Astronuat21/4DS/Images/CTRL_L/Left_Controls_Back.png

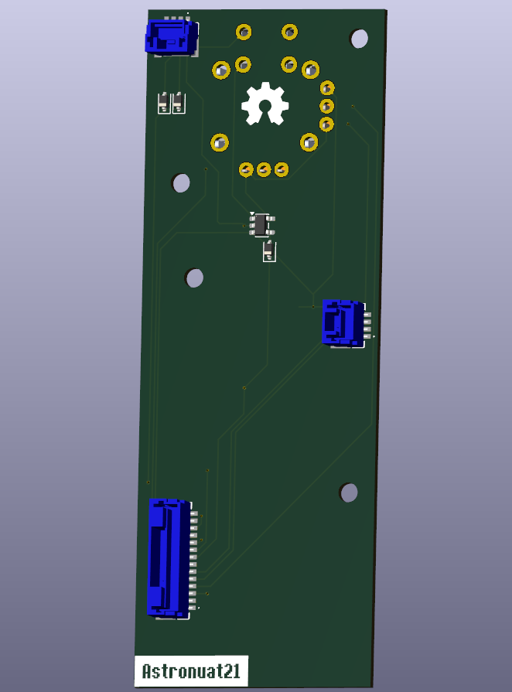
Images/CTRL_L/Left_Controls_Back.png
