Astronuat21/4DS/Images/CTRL_L/Left_Controls_PCB.png

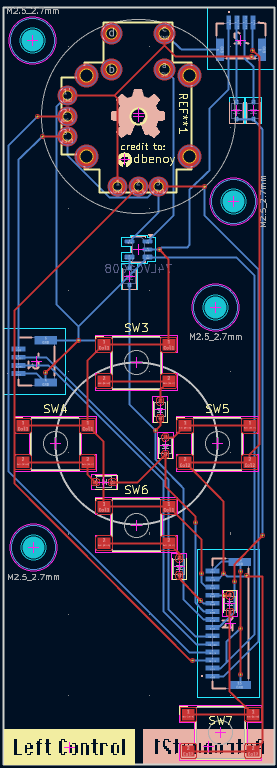
Images/CTRL_L/Left_Controls_PCB.png
