Astronuat21/4DS/Images/CTRL_R/Right_Controls_Back.png

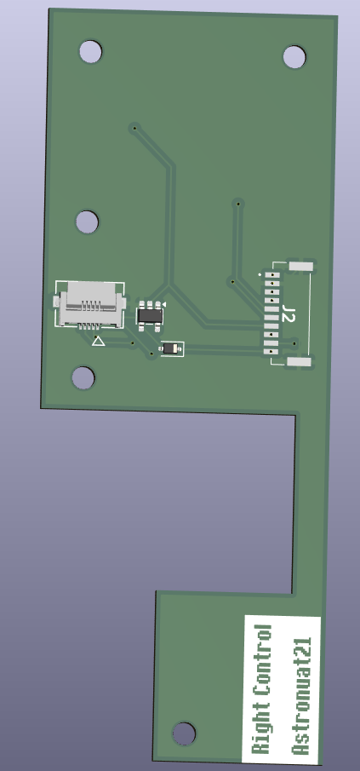
Images/CTRL_R/Right_Controls_Back.png
