Astronuat21/4DS/Images/Motherboard/PCB_Wifi_05_12_26.png

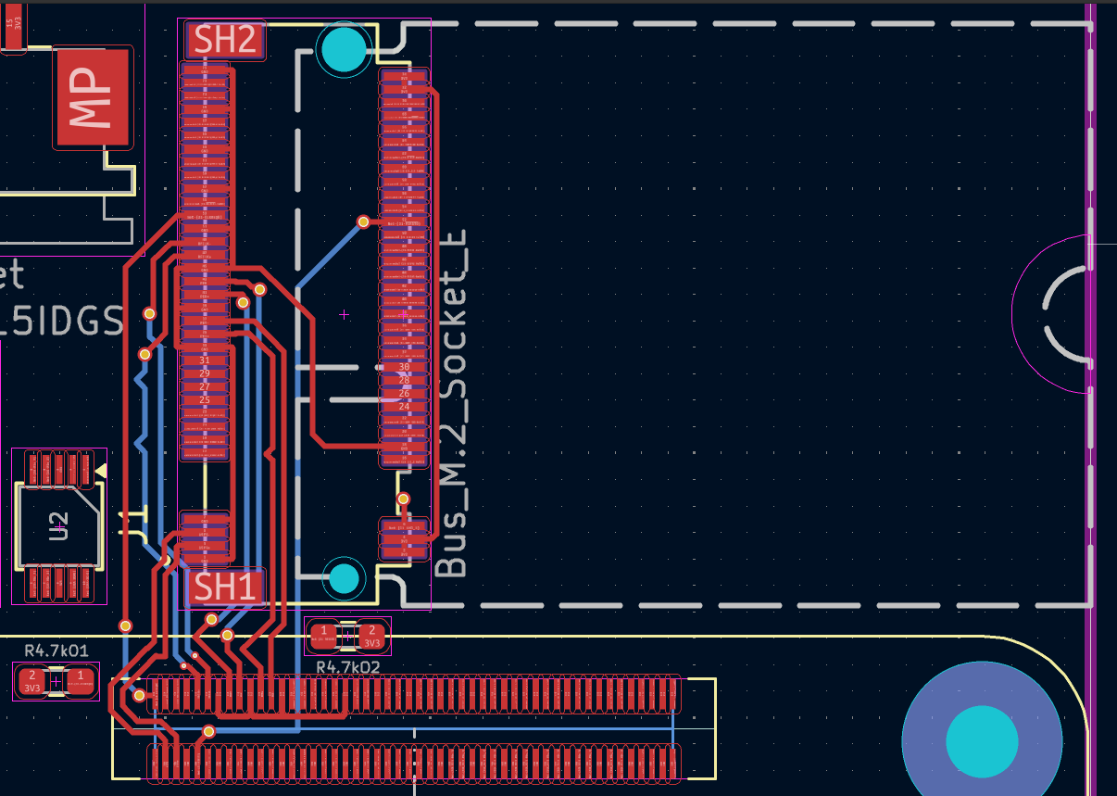
Images/Motherboard/PCB_Wifi_05_12_26.png
