Astronuat21/4DS/Images/Other/4DSPowerPath.png

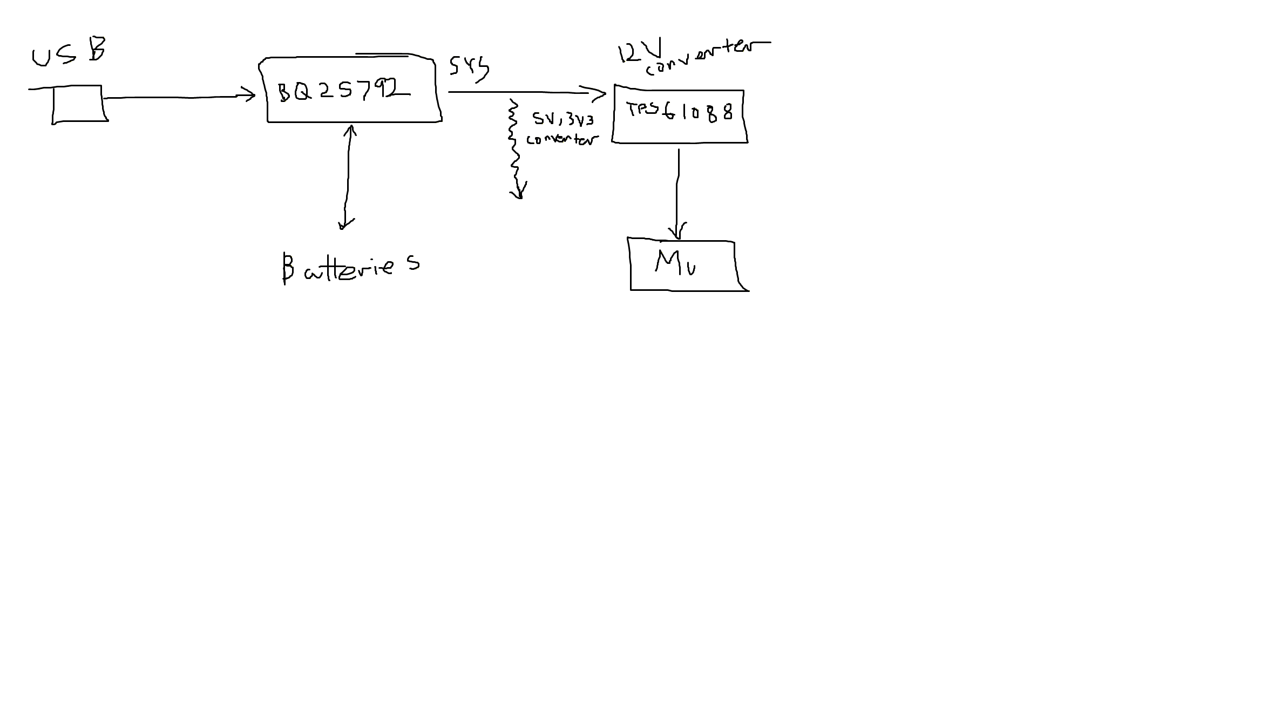
Images/Other/4DSPowerPath.png
