Astronuat21/4DS/Motherboard/3D_models/MDT420M02001.step

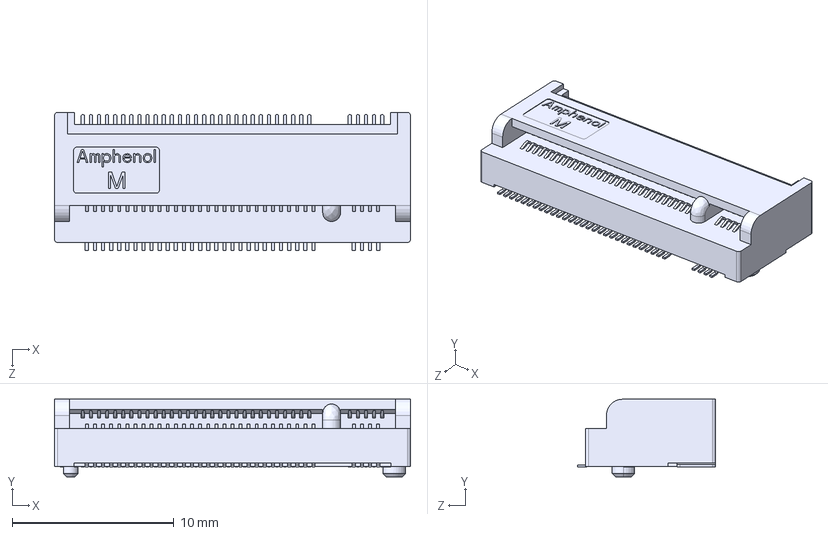
[picture p26: CAD file, 2026-07-04]
Motherboard/3D_models/MDT420M02001.step
22.0 x 4.80 x 8.55 mm
