Astronuat21/4DS/3D Models/General/LattePandaCoolerFan.stl

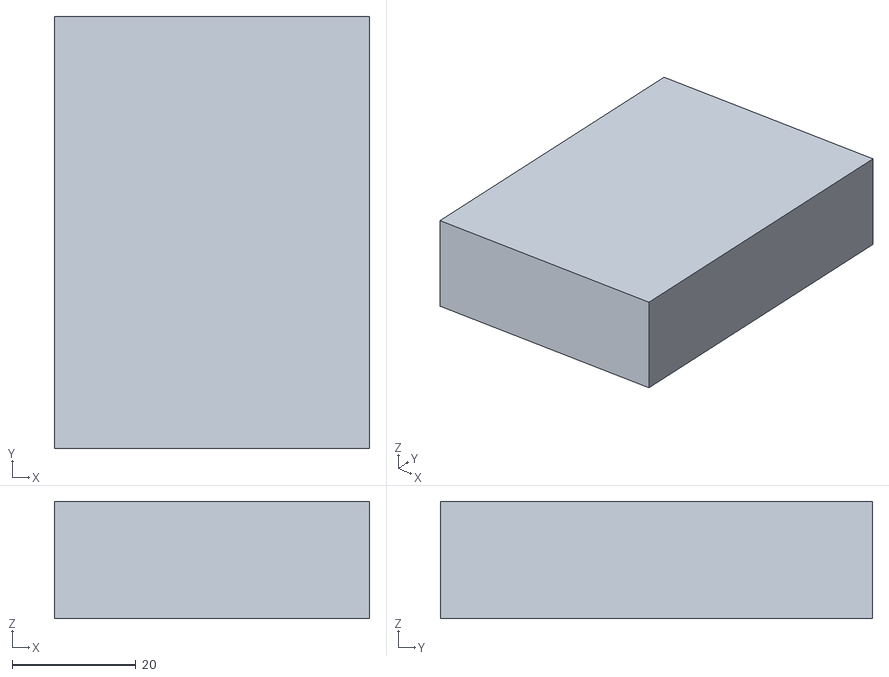
[picture p27: CAD file, 2026-06-12]
3D Models/General/LattePandaCoolerFan.stl
51.0 x 70.0 x 19.0
