Astronuat21/4DS/3D Models/ShellTest/CTRL_L_SLIDERS_JUN11.stl

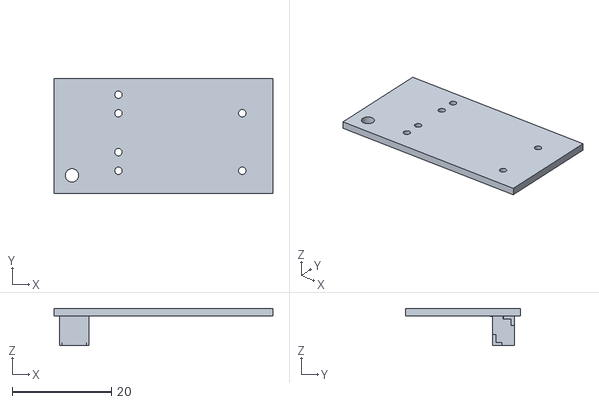
[picture p28: CAD file, 2026-06-12]
3D Models/ShellTest/CTRL_L_SLIDERS_JUN11.stl
44.2 x 23.2 x 7.54
