Astronuat21/4DS/3D Models/ShellTest/4DS Shell test 180x95x30, +2.5S F=7 B=5.obj

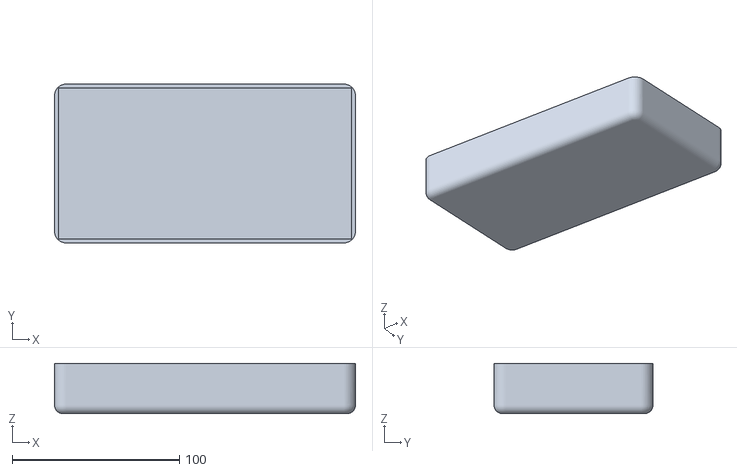
[picture p31: CAD file, 2026-05-12]
3D Models/ShellTest/4DS Shell test 180x95x30, +2.5S F=7 B=5.obj
180.0 x 95.0 x 30.0
