Astronuat21/4DS/3D Models/ShellTest/exportsettings.png

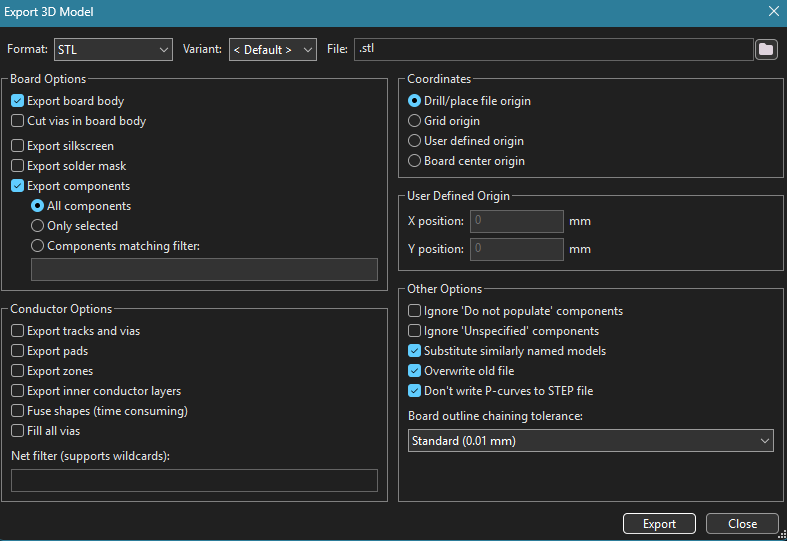
3D Models/ShellTest/exportsettings.png
